BadenLab/Open-Visual-Stimulator/Stimulator Calibration/data/Red.csv

Optical Power Monitor
1.1.2315.102
Delimiter Used:
Start of Measurement | 7/18/2019 17:33:45
Sample Interval | 1 s
 | PM100D 18112641
Type | PM100D
Serialnumber | P0009872
Sensor | S130VC
SensorSerialnumber | 18112641
Wavelength / Responsivity | 565 nm
 |  |  | PM100D 18112641
Samples | Date (MM/dd/yyyy) | Time of day (hh:mm:ss) | Power (W)
0 | 7/18/2019 | 17:33:45 | -9.3884E-10
1 | 7/18/2019 | 17:33:46 | -9.3913E-10
2 | 7/18/2019 | 17:33:47 | -9.3894E-10
3 | 7/18/2019 | 17:33:48 | -9.3916E-10
4 | 7/18/2019 | 17:33:49 | -9.3928E-10
5 | 7/18/2019 | 17:33:50 | -9.3921E-10
6 | 7/18/2019 | 17:33:51 | -9.3859E-10
7 | 7/18/2019 | 17:33:52 | -9.39E-10
8 | 7/18/2019 | 17:33:53 | -9.3884E-10
9 | 7/18/2019 | 17:33:54 | -9.3878E-10
10 | 7/18/2019 | 17:33:55 | -9.3878E-10
11 | 7/18/2019 | 17:33:56 | -9.3855E-10
12 | 7/18/2019 | 17:33:57 | -9.3844E-10
13 | 7/18/2019 | 17:33:58 | -9.3848E-10
14 | 7/18/2019 | 17:33:59 | -9.3701E-10
15 | 7/18/2019 | 17:34:00 | -9.3499E-10
16 | 7/18/2019 | 17:34:01 | -9.3199E-10
17 | 7/18/2019 | 17:34:02 | -9.2531E-10
18 | 7/18/2019 | 17:34:03 | -9.1818E-10
19 | 7/18/2019 | 17:34:04 | -9.1014E-10
20 | 7/18/2019 | 17:34:05 | -9.0089E-10
21 | 7/18/2019 | 17:34:06 | -8.9566E-10
22 | 7/18/2019 | 17:34:07 | -8.7976E-10
23 | 7/18/2019 | 17:34:08 | -8.6271E-10
24 | 7/18/2019 | 17:34:09 | -8.3909E-10
25 | 7/18/2019 | 17:34:10 | -8.1591E-10
26 | 7/18/2019 | 17:34:11 | -7.8959E-10
27 | 7/18/2019 | 17:34:12 | -7.603E-10
28 | 7/18/2019 | 17:34:13 | -7.3008E-10
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
1462 | 7/18/2019 | 17:58:07 | -9.4643E-10
1463 | 7/18/2019 | 17:58:08 | -9.465E-10
1464 | 7/18/2019 | 17:58:09 | -9.4614E-10
1465 | 7/18/2019 | 17:58:10 | -9.4593E-10
1466 | 7/18/2019 | 17:58:11 | -9.4558E-10
1467 | 7/18/2019 | 17:58:12 | -9.456E-10
1468 | 7/18/2019 | 17:58:13 | -9.4589E-10
1469 | 7/18/2019 | 17:58:14 | -9.4676E-10
1470 | 7/18/2019 | 17:58:15 | -9.4805E-10
1471 | 7/18/2019 | 17:58:16 | -9.4917E-10
1472 | 7/18/2019 | 17:58:17 | -9.5061E-10
1473 | 7/18/2019 | 17:58:18 | -9.5144E-10
1474 | 7/18/2019 | 17:58:19 | -9.5234E-10
1475 | 7/18/2019 | 17:58:20 | -9.5292E-10
1476 | 7/18/2019 | 17:58:21 | -9.5366E-10
1477 | 7/18/2019 | 17:58:22 | -9.5458E-10
1478 | 7/18/2019 | 17:58:23 | -9.5515E-10
1479 | 7/18/2019 | 17:58:24 | -9.5631E-10
1480 | 7/18/2019 | 17:58:25 | -9.5713E-10
1481 | 7/18/2019 | 17:58:26 | -9.5791E-10
1482 | 7/18/2019 | 17:58:27 | -9.5796E-10
1483 | 7/18/2019 | 17:58:28 | -9.5708E-10
