BadenLab/Open-Visual-Stimulator/Stimulator Calibration/data/UV.csv

Optical Power Monitor
1.1.2315.102
Delimiter Used:
Start of Measurement | 7/18/2019 16:11:52
Sample Interval | 1 s
 | PM100D 18112641
Type | PM100D
Serialnumber | P0009872
Sensor | S130VC
SensorSerialnumber | 18112641
Wavelength / Responsivity | 361 nm
 |  |  | PM100D 18112641
Samples | Date (MM/dd/yyyy) | Time of day (hh:mm:ss) | Power (W)
0 | 7/18/2019 | 16:11:52 | -9.1363E-11
1 | 7/18/2019 | 16:11:54 | -9.0673E-11
2 | 7/18/2019 | 16:11:55 | -9.2826E-11
3 | 7/18/2019 | 16:11:56 | -9.5724E-11
4 | 7/18/2019 | 16:11:57 | -9.8295E-11
5 | 7/18/2019 | 16:11:58 | -1.0069E-10
6 | 7/18/2019 | 16:11:59 | -1.0284E-10
7 | 7/18/2019 | 16:12:00 | -1.0507E-10
8 | 7/18/2019 | 16:12:01 | -1.0458E-10
9 | 7/18/2019 | 16:12:02 | -1.0347E-10
10 | 7/18/2019 | 16:12:03 | -1.0303E-10
11 | 7/18/2019 | 16:12:04 | -1.0274E-10
12 | 7/18/2019 | 16:12:05 | -1.0085E-10
13 | 7/18/2019 | 16:12:06 | -1.0472E-10
14 | 7/18/2019 | 16:12:07 | -1.0637E-10
15 | 7/18/2019 | 16:12:08 | -1.0912E-10
16 | 7/18/2019 | 16:12:09 | -1.1437E-10
17 | 7/18/2019 | 16:12:10 | -1.178E-10
18 | 7/18/2019 | 16:12:11 | -1.16E-10
19 | 7/18/2019 | 16:12:12 | -1.1158E-10
20 | 7/18/2019 | 16:12:13 | -1.0505E-10
21 | 7/18/2019 | 16:12:14 | -9.552E-11
22 | 7/18/2019 | 16:12:15 | -8.2076E-11
23 | 7/18/2019 | 16:12:16 | -6.4947E-11
24 | 7/18/2019 | 16:12:17 | -4.5477E-11
25 | 7/18/2019 | 16:12:18 | -2.1898E-11
26 | 7/18/2019 | 16:12:19 | 6.1107E-12
27 | 7/18/2019 | 16:12:20 | 3.7962E-11
28 | 7/18/2019 | 16:12:21 | 7.4102E-11
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
1302 | 7/18/2019 | 16:33:35 | 6.6462E-09
1303 | 7/18/2019 | 16:33:36 | 2.6201E-10
1304 | 7/18/2019 | 16:33:37 | -9.2993E-10
1305 | 7/18/2019 | 16:33:38 | -9.3382E-10
1306 | 7/18/2019 | 16:33:39 | -9.3561E-10
1307 | 7/18/2019 | 16:33:40 | -9.3794E-10
1308 | 7/18/2019 | 16:33:41 | -9.3962E-10
